Dav1dyang/Little-Ambience/Day and Night Tabletop Light/3D Prints/DandN Version 4_Stand.3mf

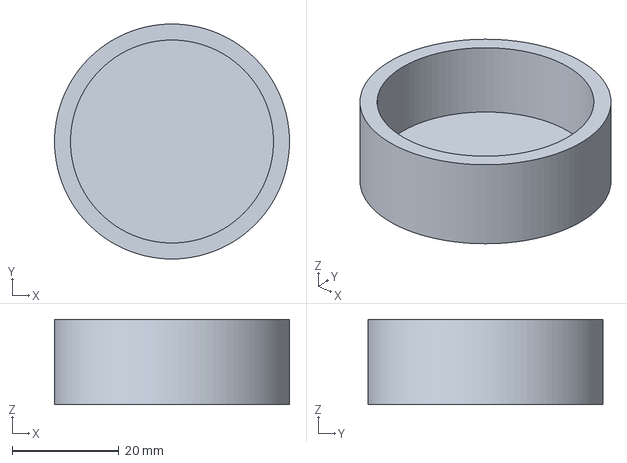
[picture p20: CAD file, 2023-08-10]
Day and Night Tabletop Light/3D Prints/DandN Version 4_Stand.3mf
44.0 x 44.0 x 16.0 mm
